Computacao-Fisica-UFSJ/projeto-final-mesmo-me-em/imagens/arduinoUno.png

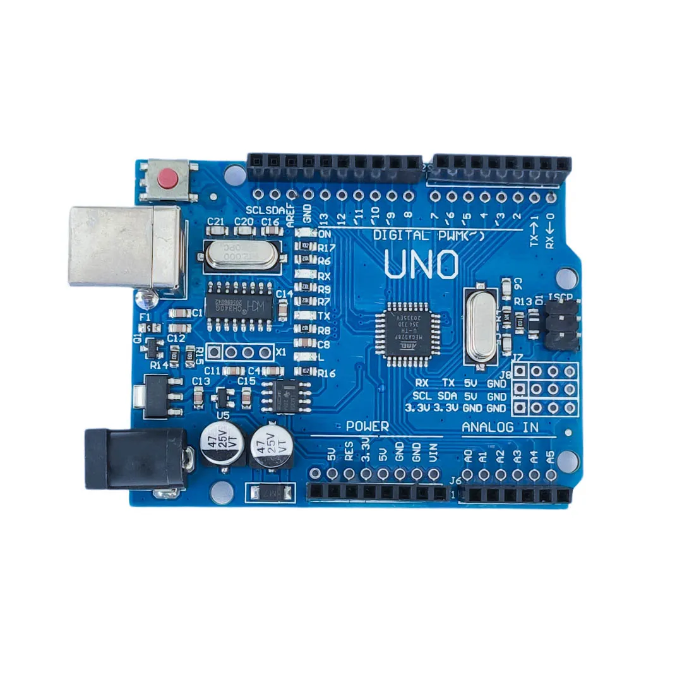
imagens/arduinoUno.png
