Computacao-Fisica-UFSJ/projeto-final-mesmo-me-em/imagens/fotoProjeto.jpg

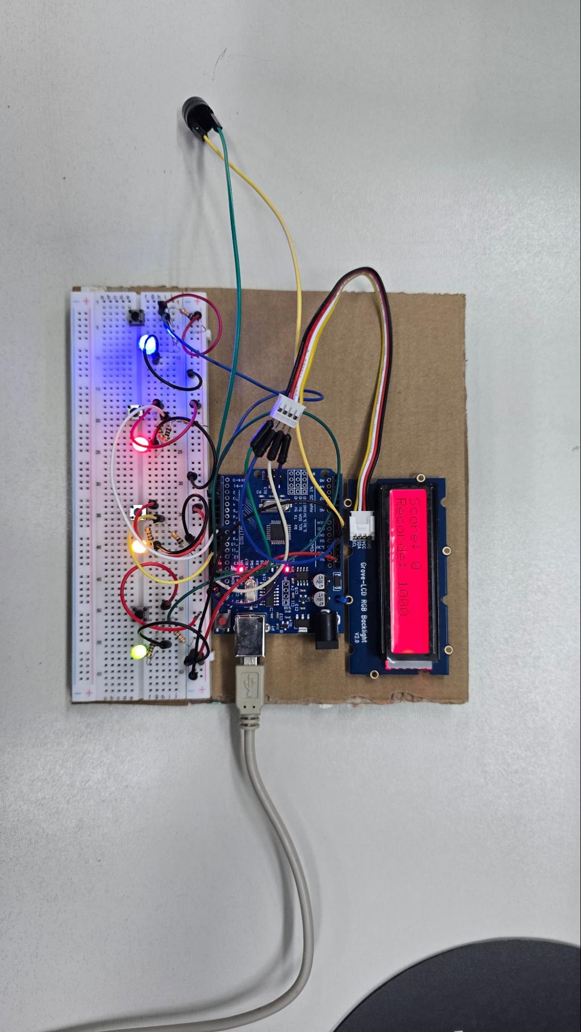
imagens/fotoProjeto.jpg
