Computacao-Fisica-UFSJ/projeto-final-mesmo-me-em/imagens/ledRGB.png

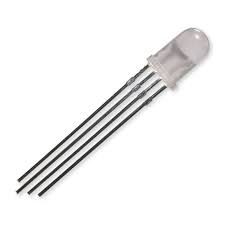
imagens/ledRGB.png
