Computacao-Fisica-UFSJ/projeto-final-mesmo-me-em/imagens/ledVermelho.png

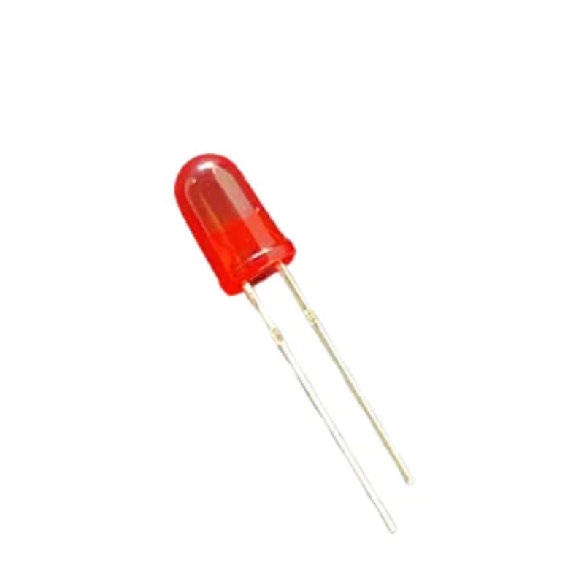
imagens/ledVermelho.png
